Koumbaya/crkbd_big_acry_case/top2.SLDPRT

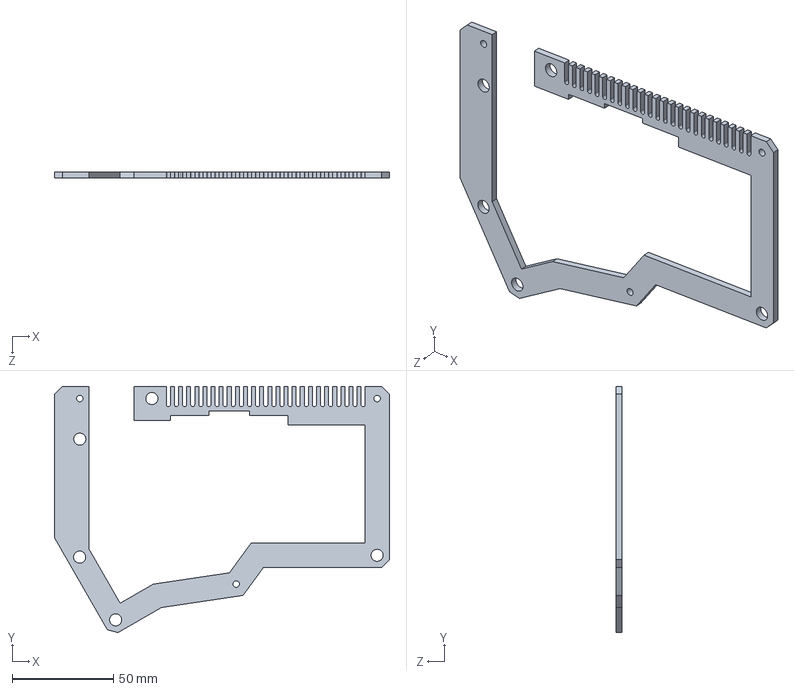
[picture p16: CAD file, 2020-07-22]
top2.SLDPRT
165.1 x 121.4 x 3.00 mm
