Koumbaya/crkbd_big_acry_case/switchplate.SLDPRT

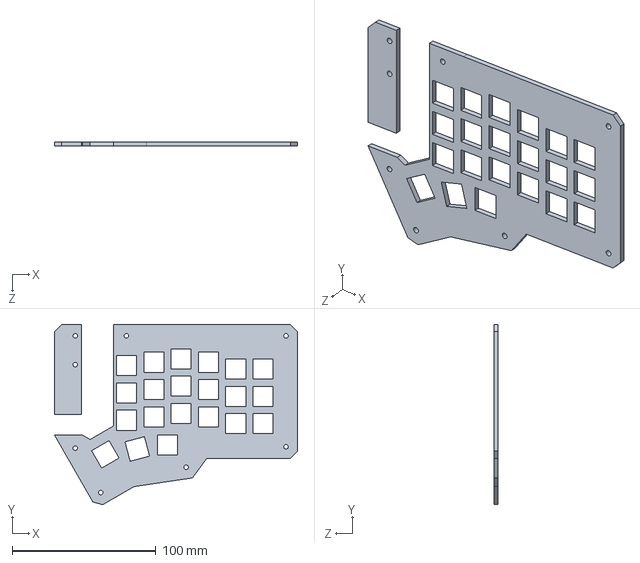
[picture p17: CAD file, 2020-07-22]
switchplate.SLDPRT
169.1 x 125.5 x 3.00 mm
